jmenzies280/embryo-monitoring/media/grid.jpg

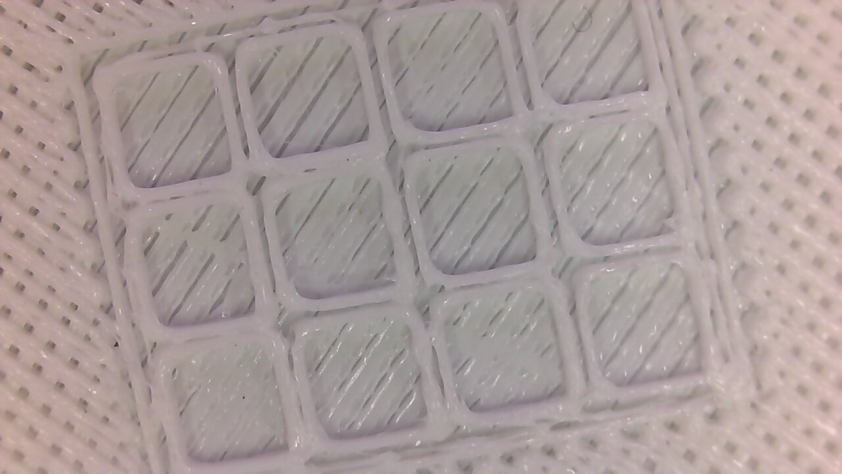
media/grid.jpg
