jmenzies280/embryo-monitoring/media/Image of embryo.png

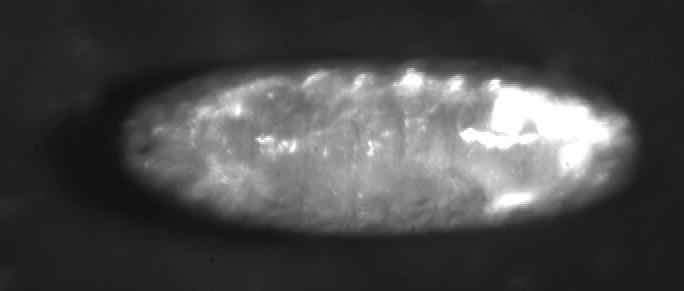
media/Image of embryo.png
