jmenzies280/embryo-monitoring/media/Screenshot at 2021-05-06 15-15-22.png

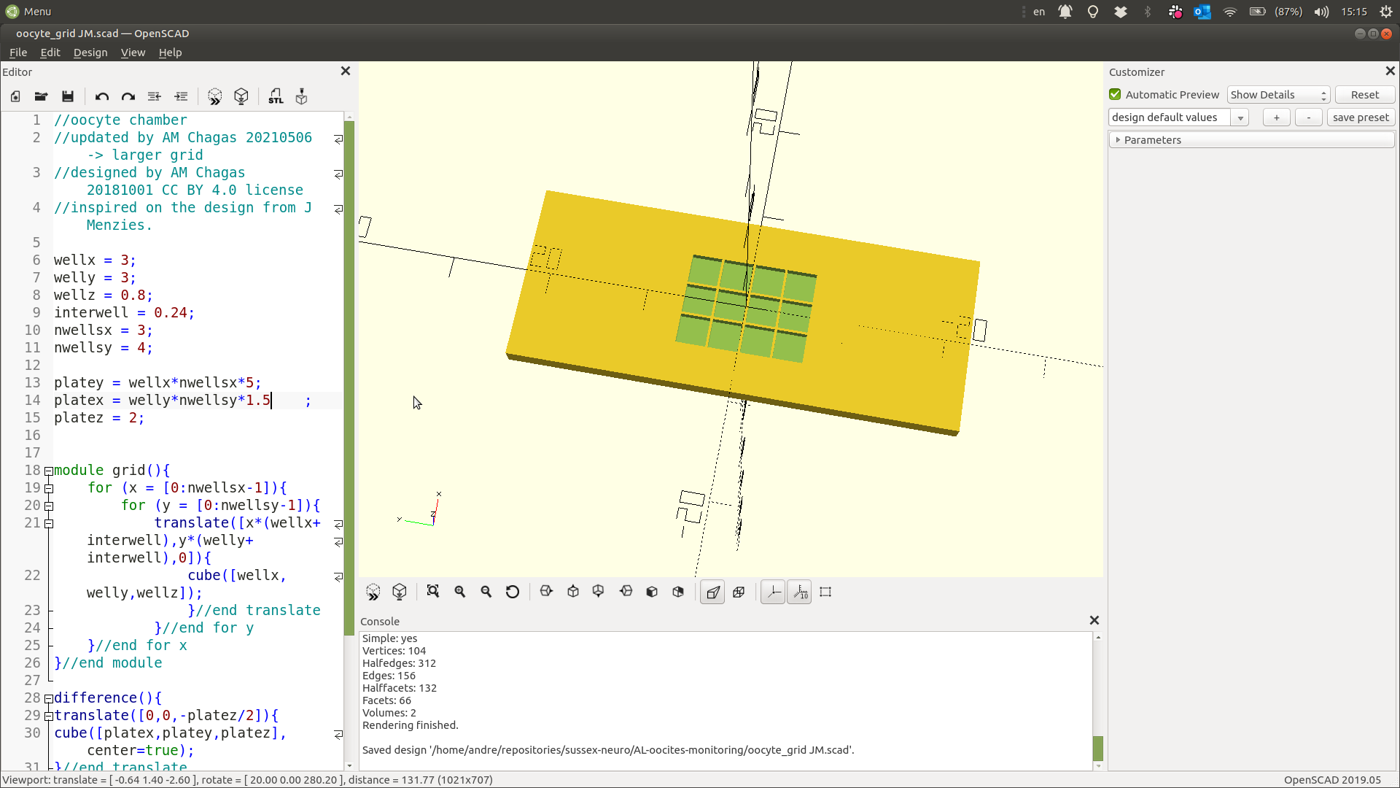
media/Screenshot at 2021-05-06 15-15-22.png
